stevenbennett/DIYson/DIYson/Printed Parts/STL/Increase Brightness Button.stl

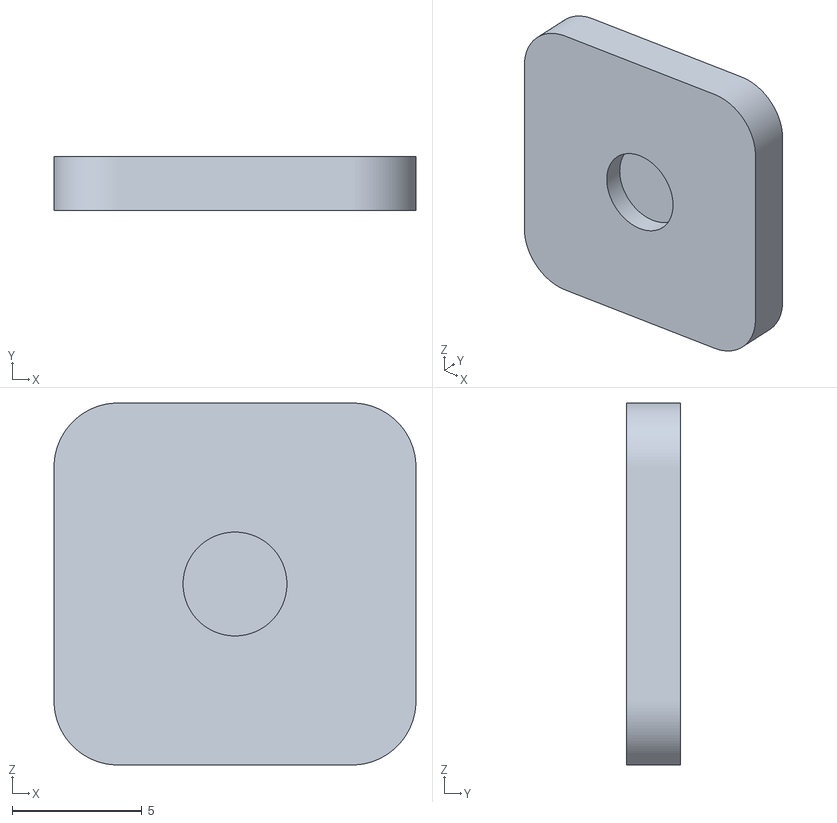
[picture p16: CAD file, 2023-01-05]
DIYson/Printed Parts/STL/Increase Brightness Button.stl
13.9 x 2.10 x 13.9
