stevenbennett/DIYson/DIYson Express/Printed Parts/STEP/Carriage Belt Clip.step

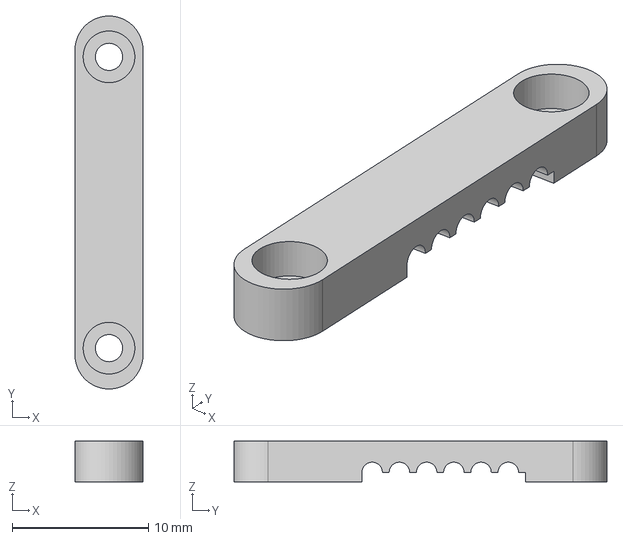
[picture p18: CAD file, 2023-01-31]
DIYson Express/Printed Parts/STEP/Carriage Belt Clip.step
5.00 x 27.4 x 3.00 mm
