stevenbennett/DIYson/DIYson Express/Printed Parts/STL/Counterweight Flex Tab (2x).stl

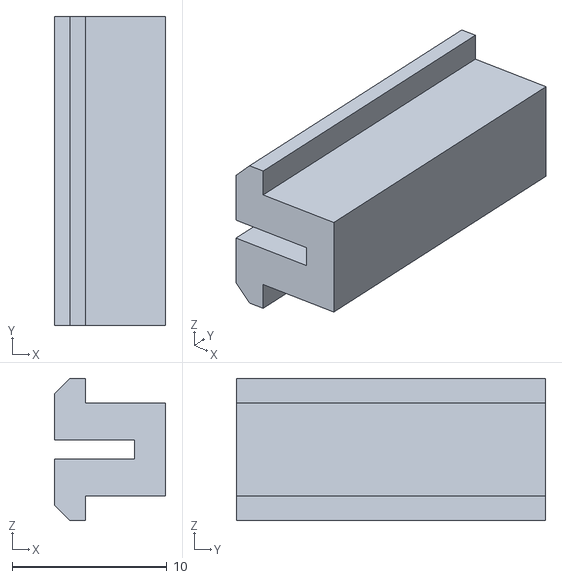
[picture p19: CAD file, 2023-01-30]
DIYson Express/Printed Parts/STL/Counterweight Flex Tab (2x).stl
7.20 x 20.0 x 9.20
