stevenbennett/DIYson/DIYson/Printed Parts/STEP/Counterweight Belt Clip.step

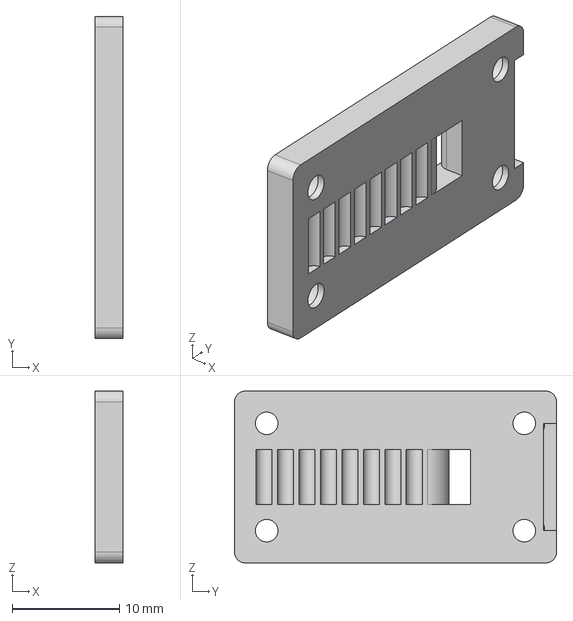
[picture p20: CAD file, 2023-01-31]
DIYson/Printed Parts/STEP/Counterweight Belt Clip.step
2.60 x 30.0 x 16.0 mm
