stevenbennett/DIYson/DIYson/Printed Parts/STL/Power Button Socket.stl

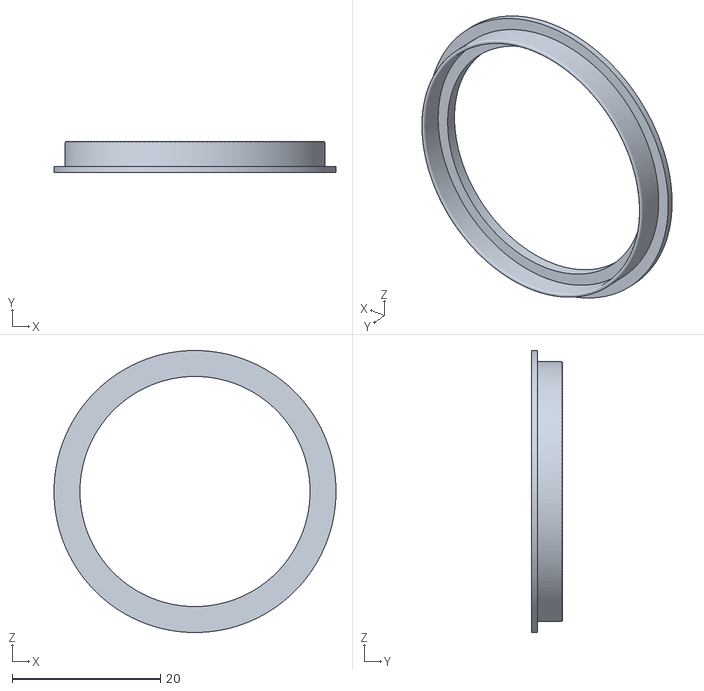
[picture p21: CAD file, 2023-01-05]
DIYson/Printed Parts/STL/Power Button Socket.stl
38.0 x 4.20 x 38.0
