stevenbennett/DIYson/DIYson Express/Printed Parts/STEP/Pulley Mount.step

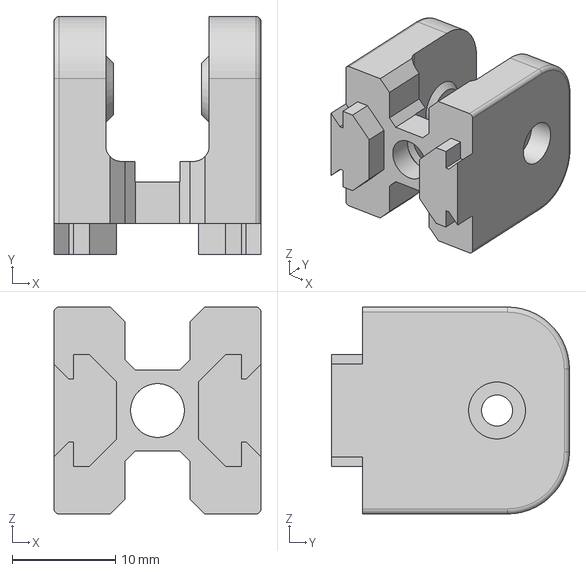
[picture p22: CAD file, 2023-01-31]
DIYson Express/Printed Parts/STEP/Pulley Mount.step
20.0 x 23.0 x 20.0 mm
