stevenbennett/DIYson/DIYson/Printed Parts/STL/Decrease Brightness Button.stl

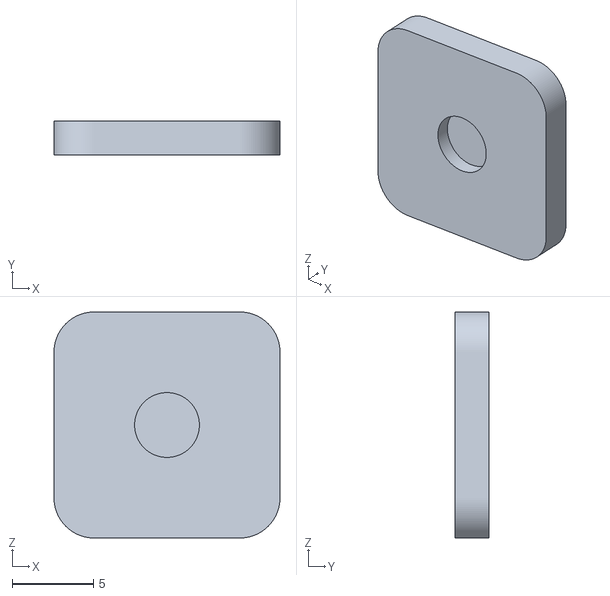
[picture p23: CAD file, 2023-01-05]
DIYson/Printed Parts/STL/Decrease Brightness Button.stl
13.9 x 2.10 x 14.0
