stevenbennett/DIYson/DIYson/Printed Parts/STEP/Drag Chain (16 links, print-in-place).stl

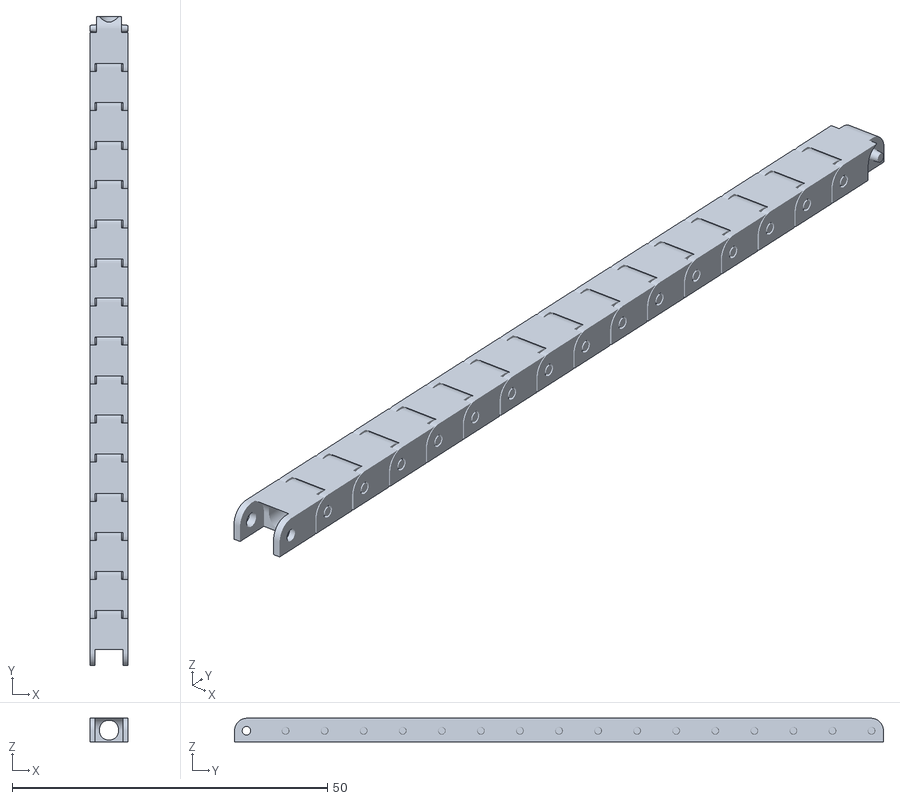
[picture p24: CAD file, 2023-01-05]
DIYson/Printed Parts/STEP/Drag Chain (16 links, print-in-place).stl
6.00 x 103.0 x 3.75
