stevenbennett/DIYson/DIYson/Printed Parts/STL/Brightness Button Socket.stl

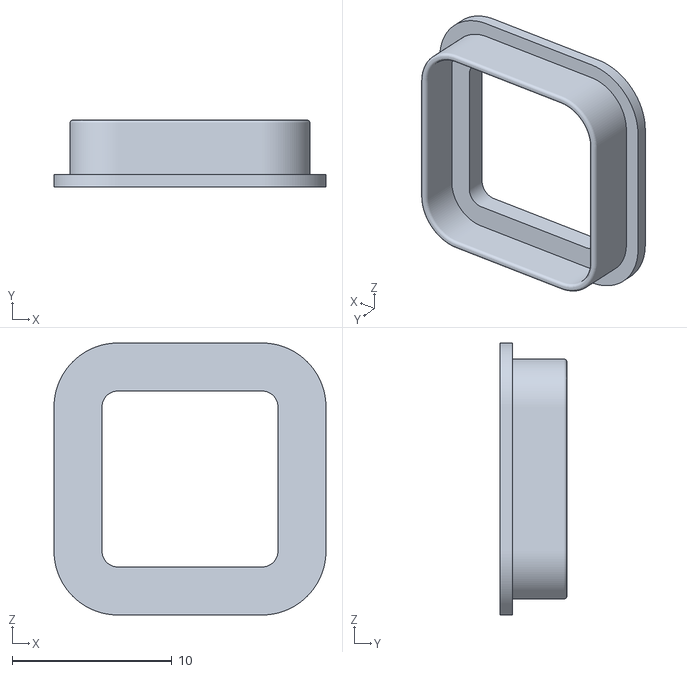
[picture p25: CAD file, 2023-01-05]
DIYson/Printed Parts/STL/Brightness Button Socket.stl
17.0 x 4.20 x 17.0
