stevenbennett/DIYson/DIYson Express/Printed Parts/STEP/Carriage.step

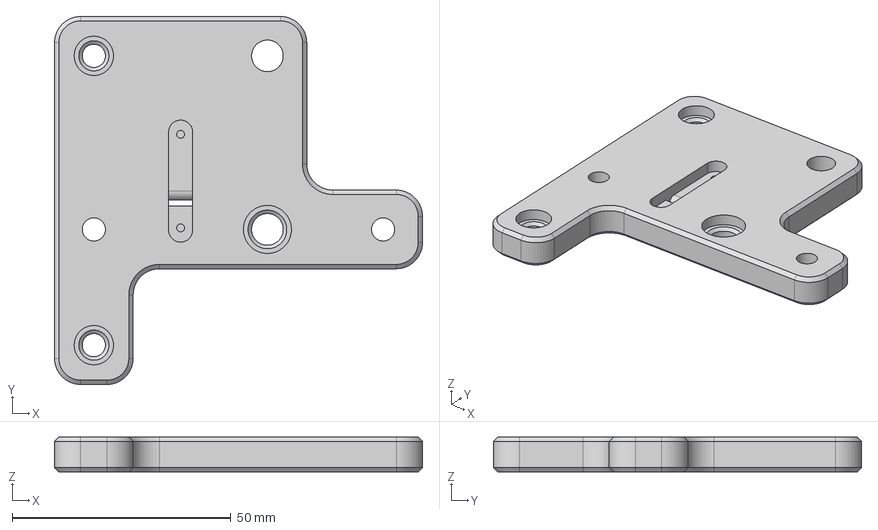
[picture p26: CAD file, 2023-01-31]
DIYson Express/Printed Parts/STEP/Carriage.step
84.2 x 84.2 x 8.00 mm
