stevenbennett/DIYson/DIYson/Printed Parts/STEP/Base.step

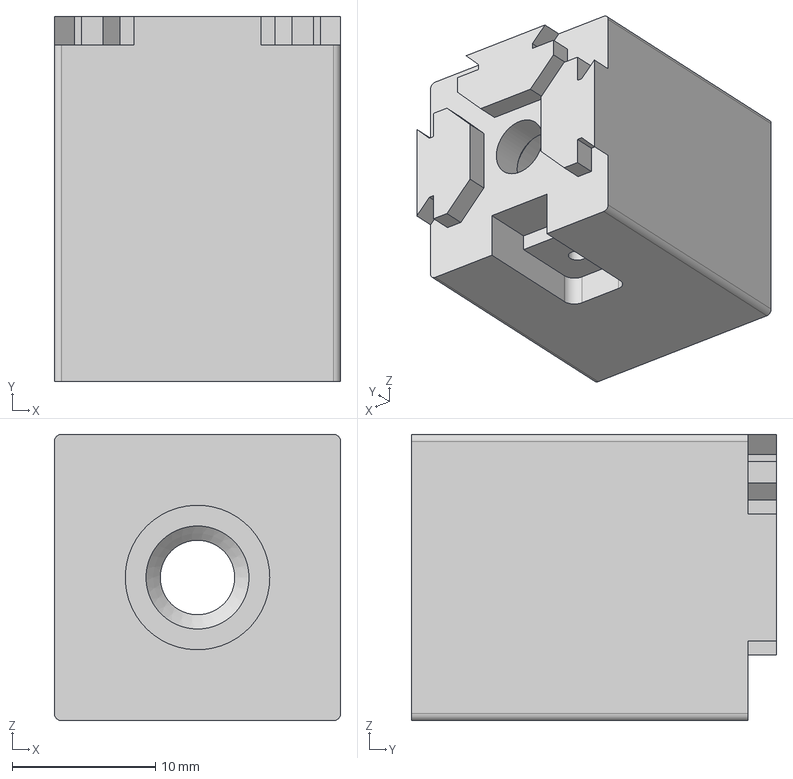
[picture p27: CAD file, 2023-01-05]
DIYson/Printed Parts/STEP/Base.step
20.0 x 25.5 x 20.0 mm
