stevenbennett/DIYson/DIYson/Printed Parts/STEP/Button Sockets.step

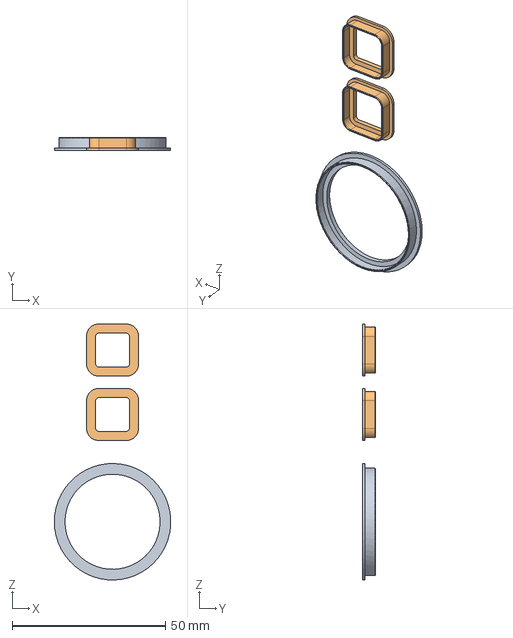
[picture p28: CAD file, 2023-01-05]
DIYson/Printed Parts/STEP/Button Sockets.step
38.0 x 4.20 x 83.5 mm
