stevenbennett/DIYson/DIYson/Printed Parts/STEP/Drag Chain Termination (Base).step

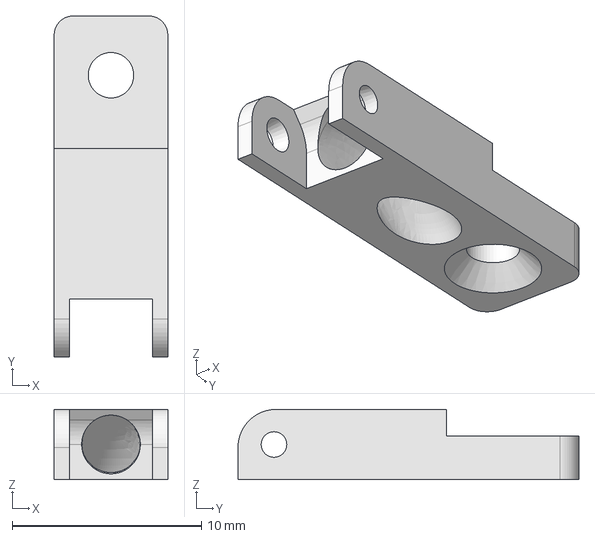
[picture p29: CAD file, 2023-01-05]
DIYson/Printed Parts/STEP/Drag Chain Termination (Base).step
6.00 x 18.0 x 3.70 mm
