stevenbennett/DIYson/DIYson Express/Printed Parts/STEP/Desk Mount.step

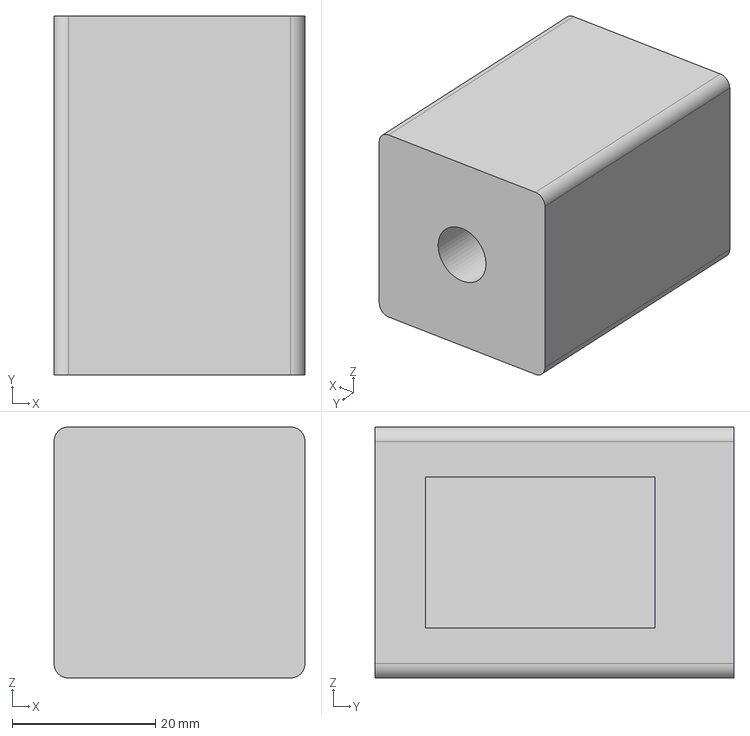
[picture p30: CAD file, 2023-01-31]
DIYson Express/Printed Parts/STEP/Desk Mount.step
35.0 x 50.0 x 35.0 mm
