stevenbennett/DIYson/DIYson/Printed Parts/STEP/LED Cover Cable Strain Relief Clip.step

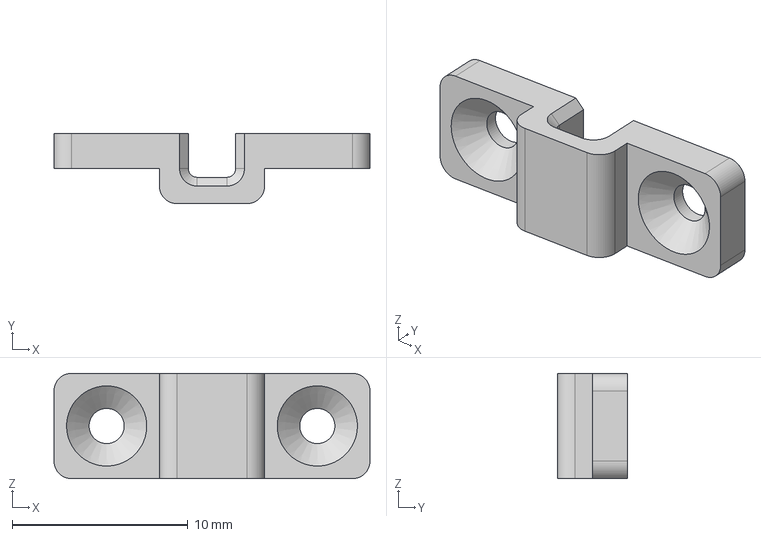
[picture p31: CAD file, 2023-01-05]
DIYson/Printed Parts/STEP/LED Cover Cable Strain Relief Clip.step
18.0 x 4.00 x 6.00 mm
