stevenbennett/DIYson/DIYson/Printed Parts/STEP/Buttons.step

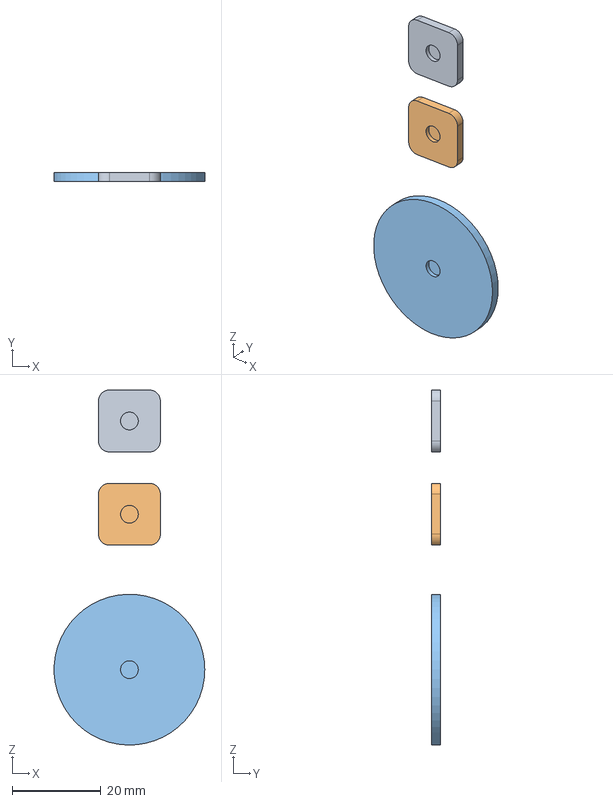
[picture p32: CAD file, 2023-01-05]
DIYson/Printed Parts/STEP/Buttons.step
33.9 x 2.10 x 79.9 mm
