stevenbennett/DIYson/DIYson/Printed Parts/STEP/LED Cover Drag Chain Termination.step

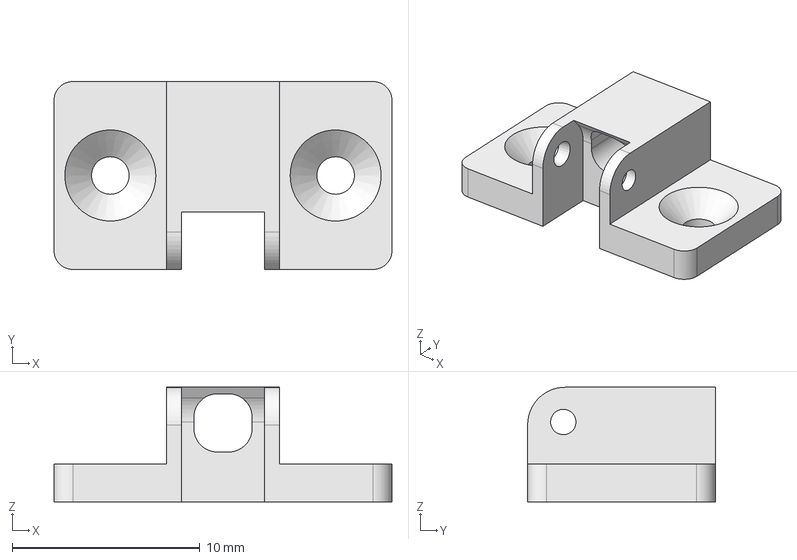
[picture p33: CAD file, 2023-01-05]
DIYson/Printed Parts/STEP/LED Cover Drag Chain Termination.step
18.0 x 10.0 x 6.10 mm
