stevenbennett/DIYson/DIYson/Printed Parts/STEP/LED Cover - Top.step

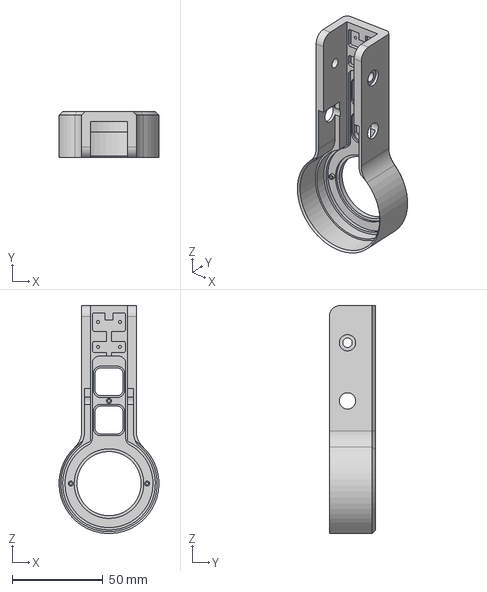
[picture p34: CAD file, 2023-01-05]
DIYson/Printed Parts/STEP/LED Cover - Top.step
55.0 x 25.5 x 125.4 mm
