stevenbennett/DIYson/DIYson/Printed Parts/STEP/Drag Chain Carriage Clip.step

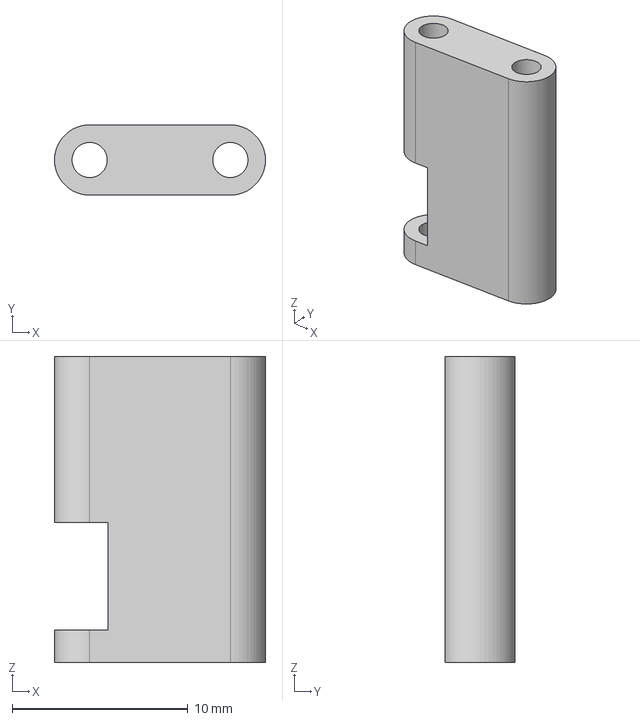
[picture p35: CAD file, 2022-10-18]
DIYson/Printed Parts/STEP/Drag Chain Carriage Clip.step
12.0 x 4.00 x 17.4 mm
