stevenbennett/DIYson/DIYson/Printed Parts/STEP/Drag Chain Link.step

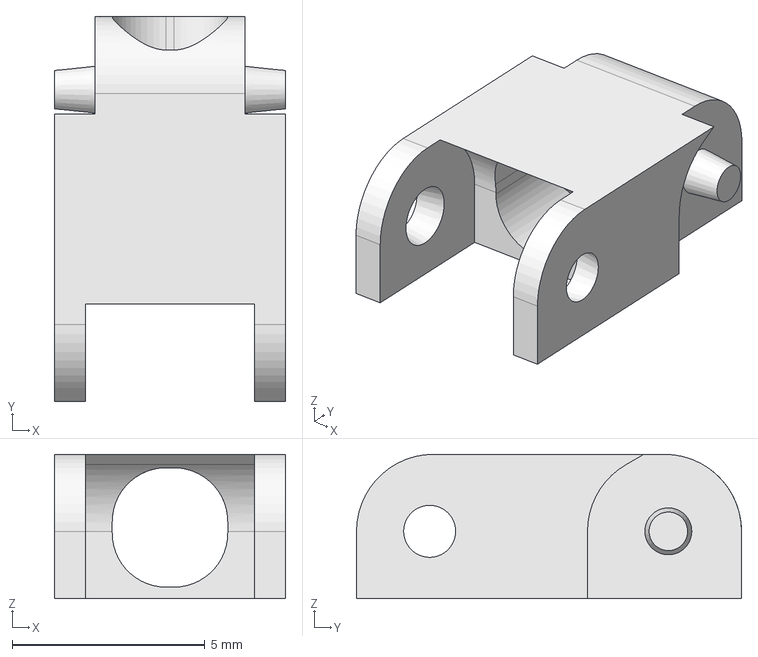
[picture p36: CAD file, 2022-10-18]
DIYson/Printed Parts/STEP/Drag Chain Link.step
6.00 x 10.0 x 3.75 mm
