stevenbennett/DIYson/DIYson/Printed Parts/STEP/Routed Spacer.step

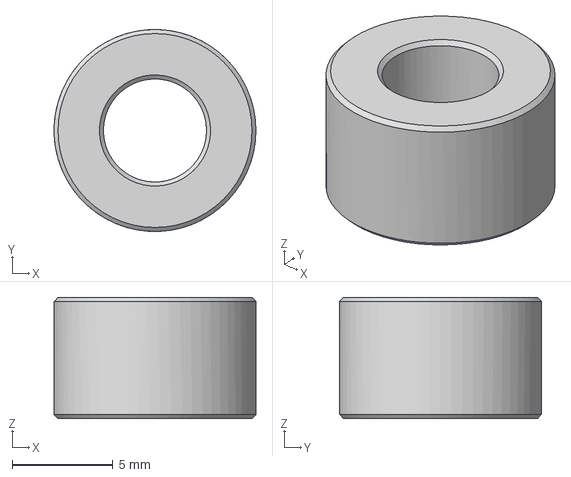
[picture p37: CAD file, 2022-10-18]
DIYson/Printed Parts/STEP/Routed Spacer.step
10.0 x 10.00 x 6.00 mm
