stevenbennett/DIYson/DIYson/Printed Parts/STEP/LED Cover - Bottom.step

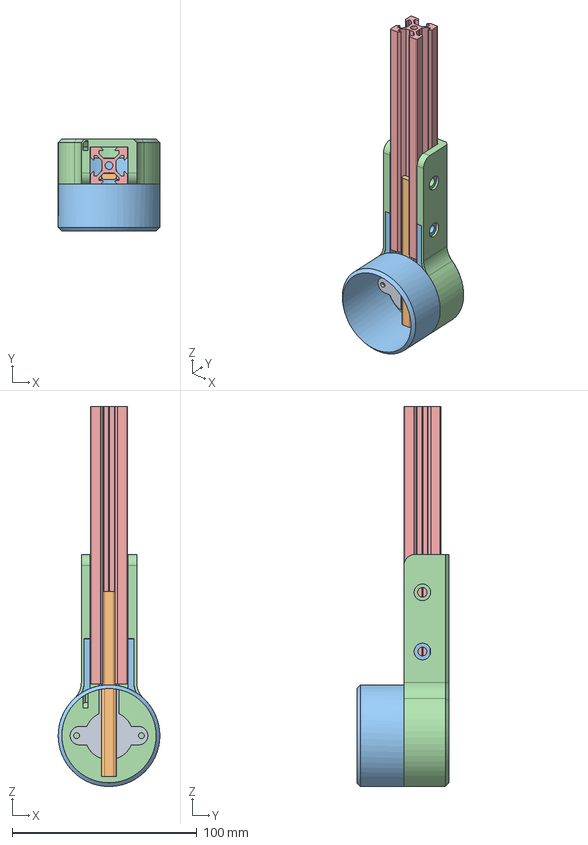
[picture p39: CAD file, 2022-08-10]
DIYson/Printed Parts/STEP/LED Cover - Bottom.step
55.0 x 50.0 x 205.5 mm
Lighting Assembly Mount
Heat pipe
