stevenbennett/DIYson/DIYson/Printed Parts/STEP/Counterweight - Flex Tab.step

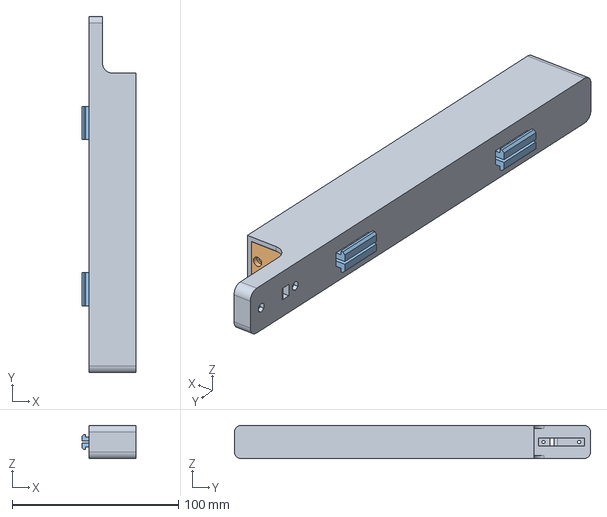
[picture p40: CAD file, 2022-08-10]
DIYson/Printed Parts/STEP/Counterweight - Flex Tab.step
32.2 x 214.0 x 20.0 mm
Counterweight
Lid
